BBBlairLiu/CITS5506_Group_Project/firmware/SmartSanESP32/secrets.example.h

#pragma once

// Copy this file to secrets.h and replace the placeholder values before upload.
// Do not commit secrets.h.

#define BLYNK_TEMPLATE_ID "REPLACE_WITH_TEMPLATE_ID"
#define BLYNK_AUTH_TOKEN "REPLACE_WITH_DEVICE_AUTH_TOKEN"

const char WIFI_SSID[] = "REPLACE_WITH_WIFI_NAME";
const char WIFI_PASS[] = "REPLACE_WITH_WIFI_PASSWORD";
